opencarecc/inpe/pictures/2017-11-20_143149.png

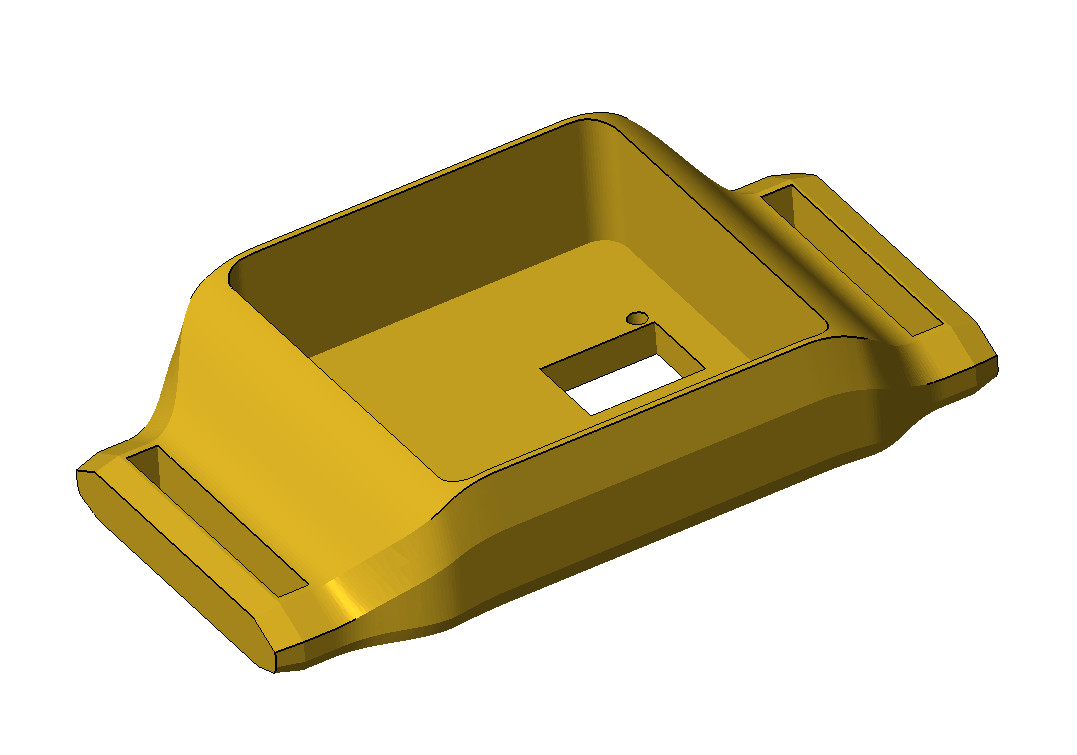
pictures/2017-11-20_143149.png
