opencarecc/inpe/pictures/2017-11-20_143255.png

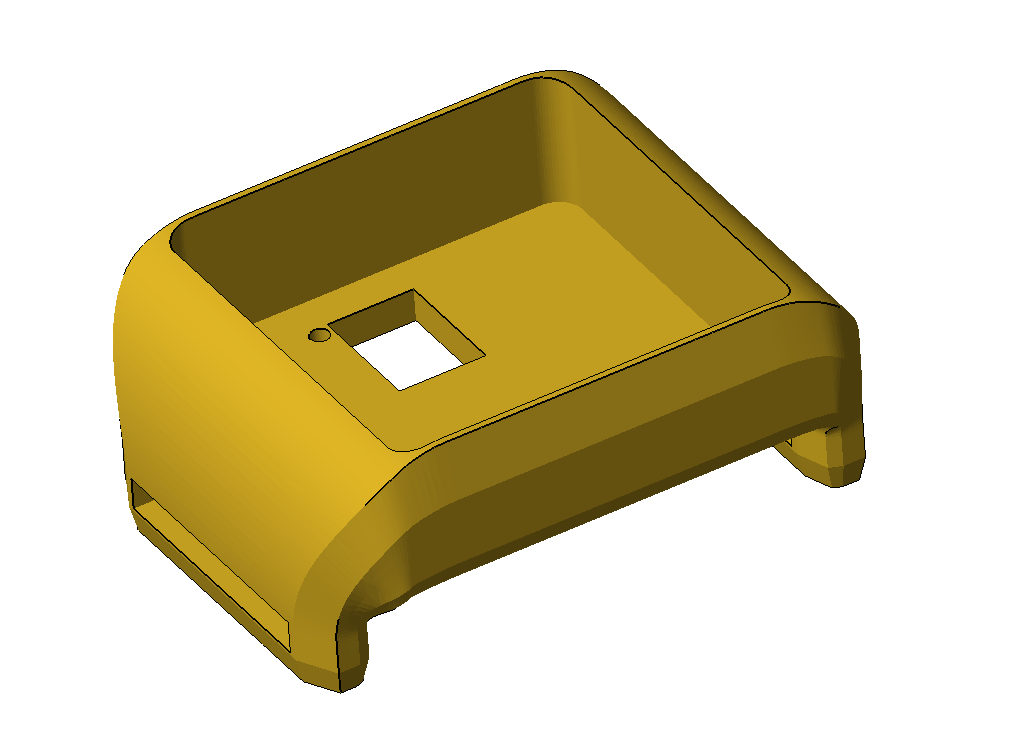
pictures/2017-11-20_143255.png
