opencarecc/inpe/pictures/_MG_9356.jpg

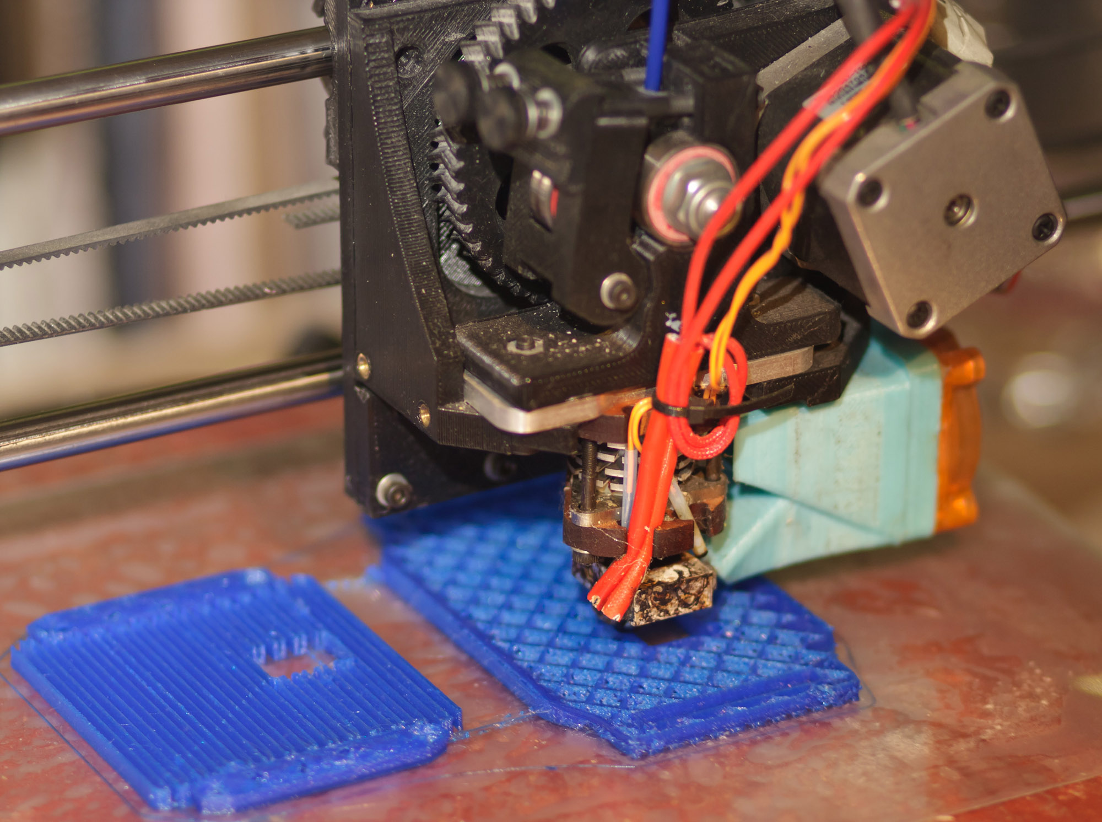
pictures/_MG_9356.jpg
