opencarecc/inpe/pictures/IMG_20171115_184903.jpeg

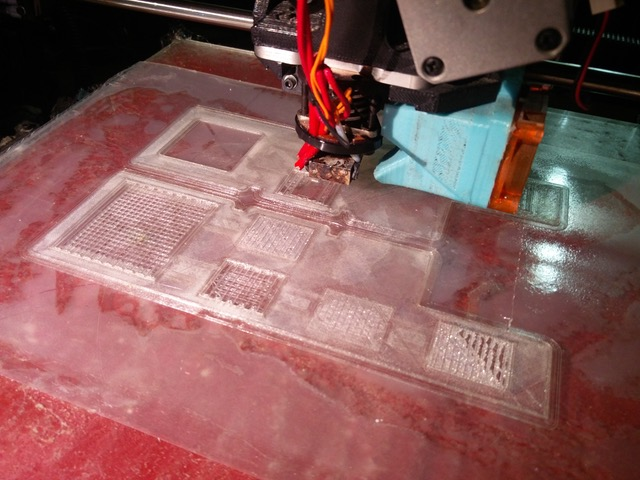
pictures/IMG_20171115_184903.jpeg
