opencarecc/inpe/pictures/IMG_20171116_113700.jpeg

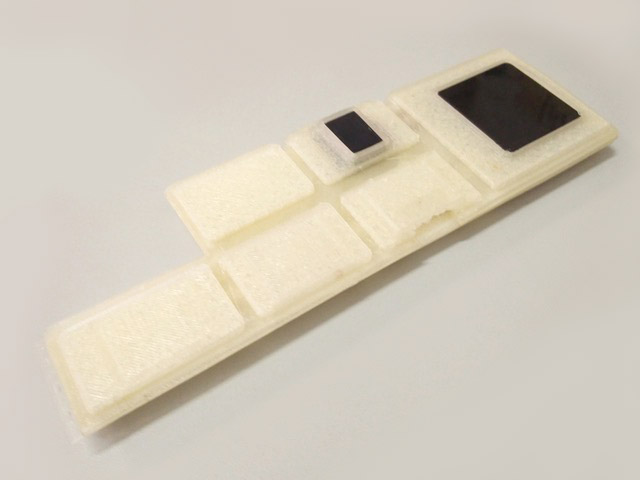
pictures/IMG_20171116_113700.jpeg
