opencarecc/inpe/pictures/IMG_20171116_195911.jpeg

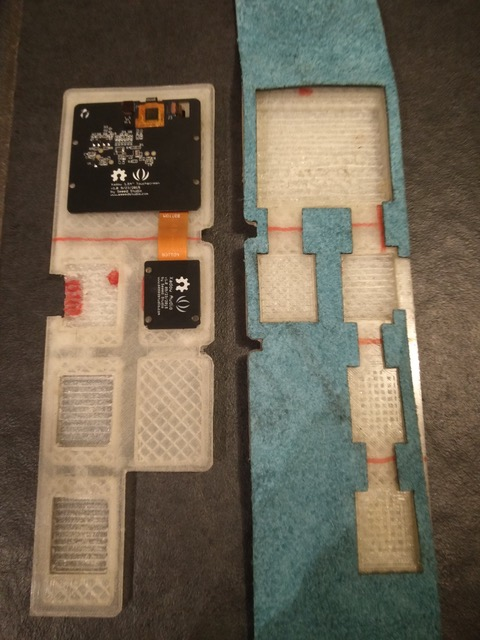
pictures/IMG_20171116_195911.jpeg
