opencarecc/inpe/pictures/InPe Layer 01.png

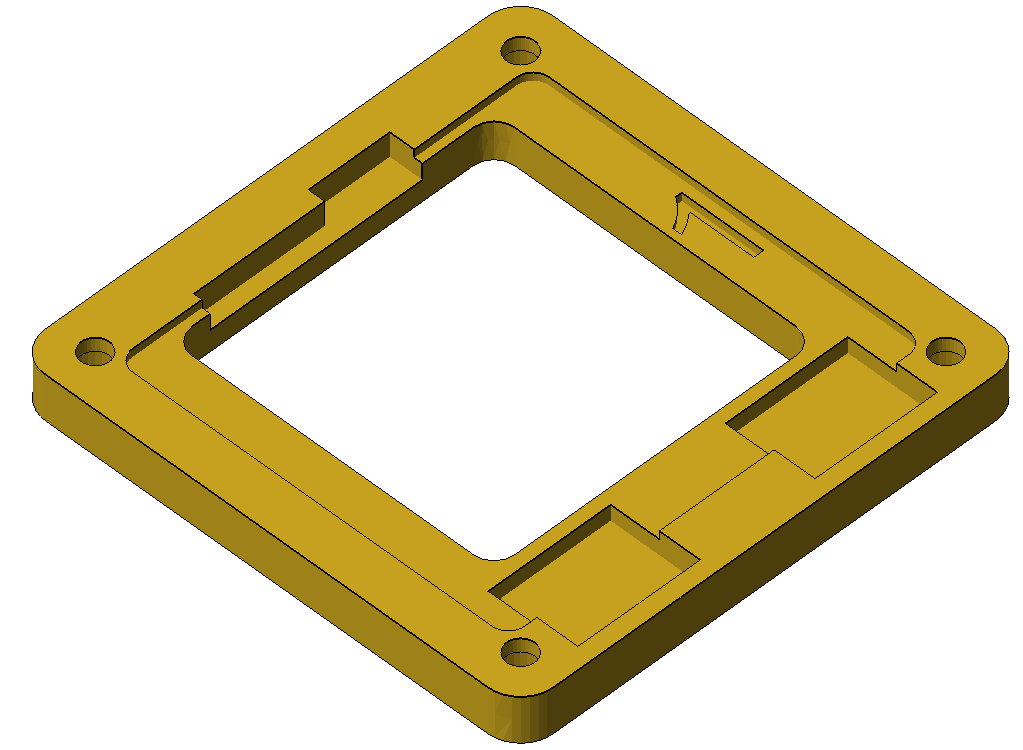
pictures/InPe Layer 01.png
