opencarecc/inpe/pictures/InPe Layer 03.png

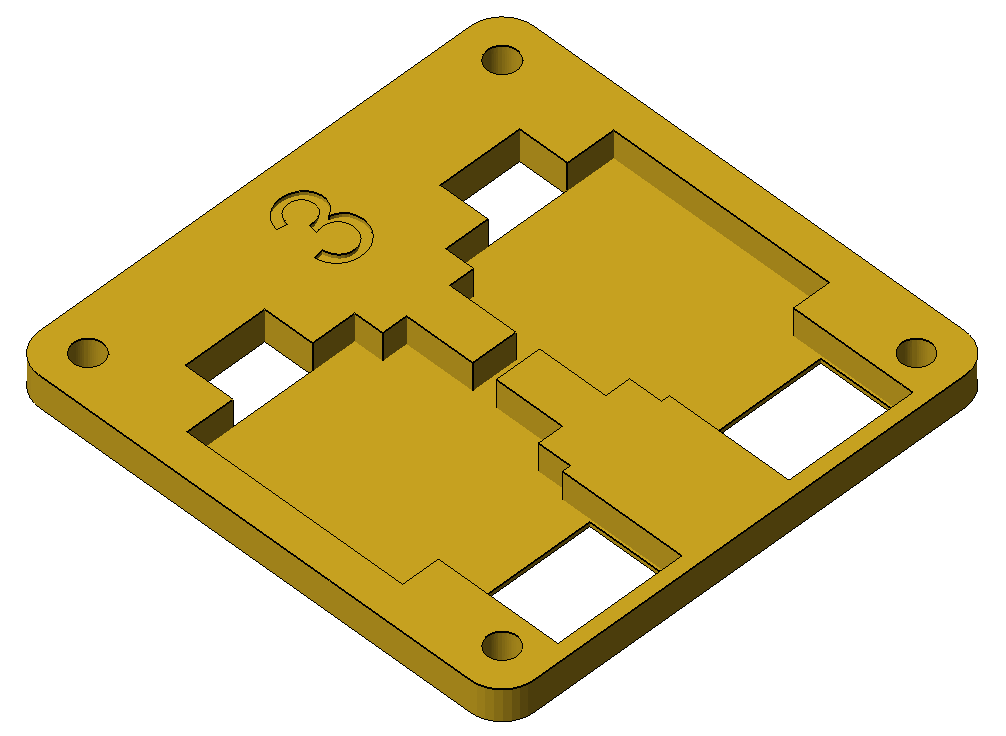
pictures/InPe Layer 03.png
