opencarecc/inpe/pictures/InPe Layer 06.png

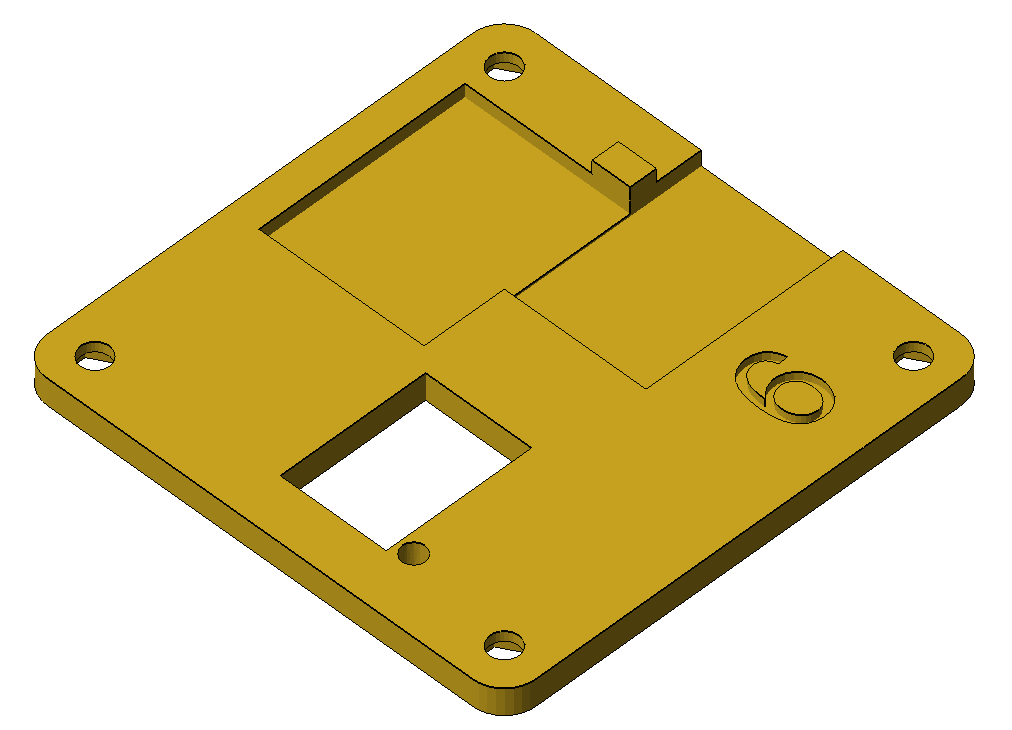
pictures/InPe Layer 06.png
