opencarecc/inpe/pictures/Inpe_Leather1.jpg

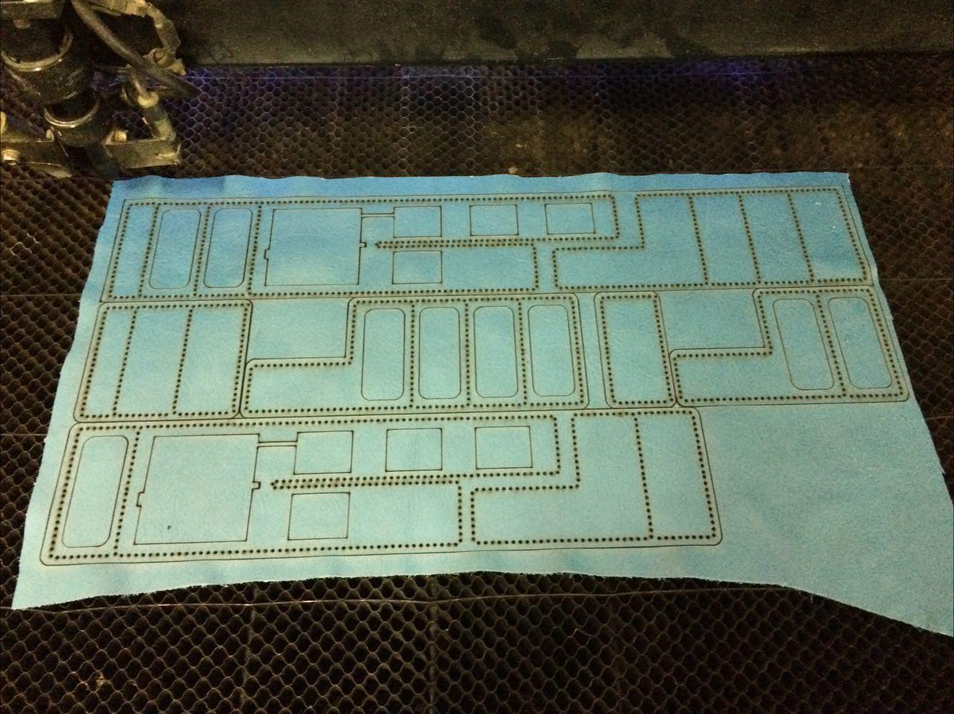
pictures/Inpe_Leather1.jpg
