opencarecc/inpe/pictures/Screen Shot 2017-11-15 at 20.32.24.png

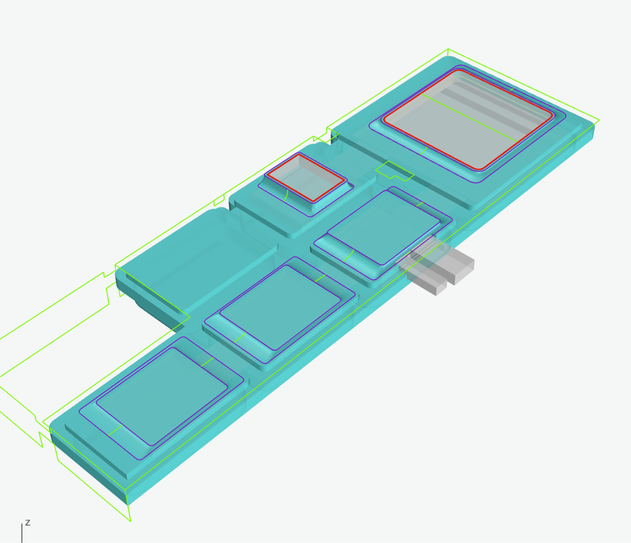
pictures/Screen Shot 2017-11-15 at 20.32.24.png
